bitsandpixels-io/rfid-jukebox/stl/wire_clamp.stl

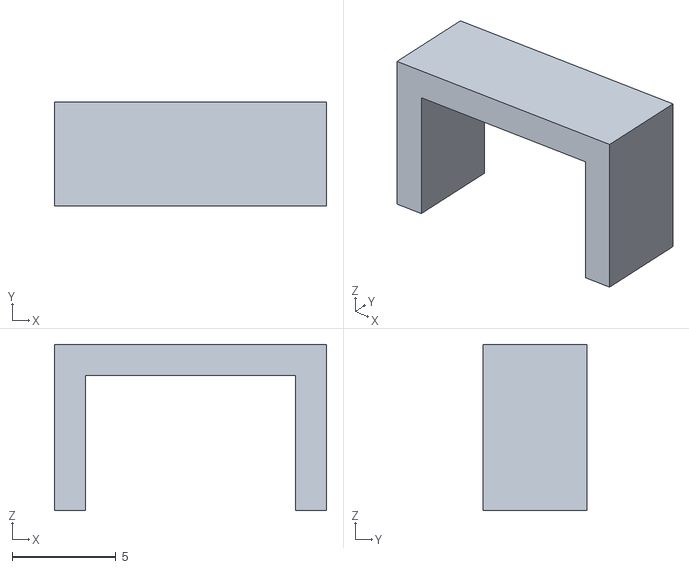
[picture p24: CAD file, 2025-07-04]
stl/wire_clamp.stl
13.1 x 5.00 x 8.00
