bitsandpixels-io/rfid-jukebox/stl/display-case-ControllerCase front.stl

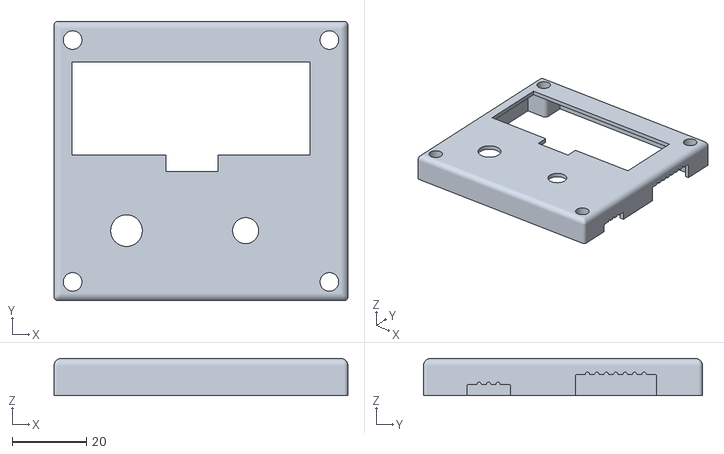
[picture p25: CAD file, 2025-07-04]
stl/display-case-ControllerCase front.stl
79.0 x 75.0 x 10.0
