bitsandpixels-io/rfid-jukebox/stl/wall_segment.stl

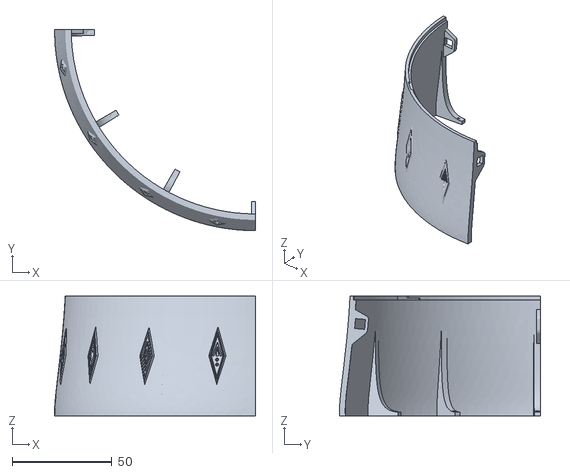
[picture p26: CAD file, 2025-07-04]
stl/wall_segment.stl
100.5 x 100.7 x 60.0
